jwcxz/bcard/boards/bcard/bcard-brd.png

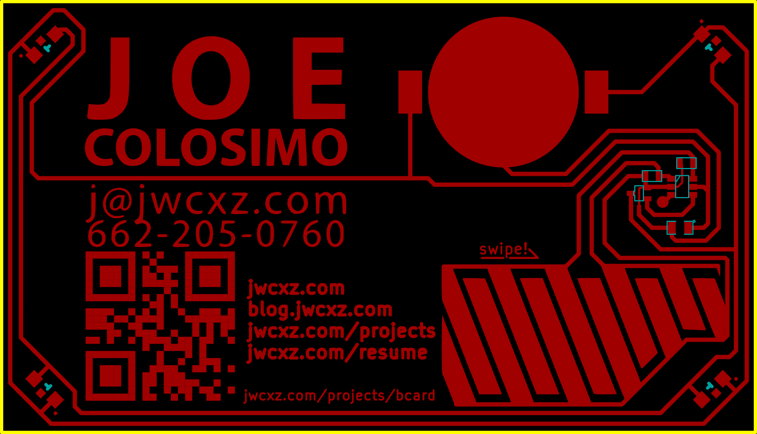
boards/bcard/bcard-brd.png
