jwcxz/bcard/imprint/name-mask.png

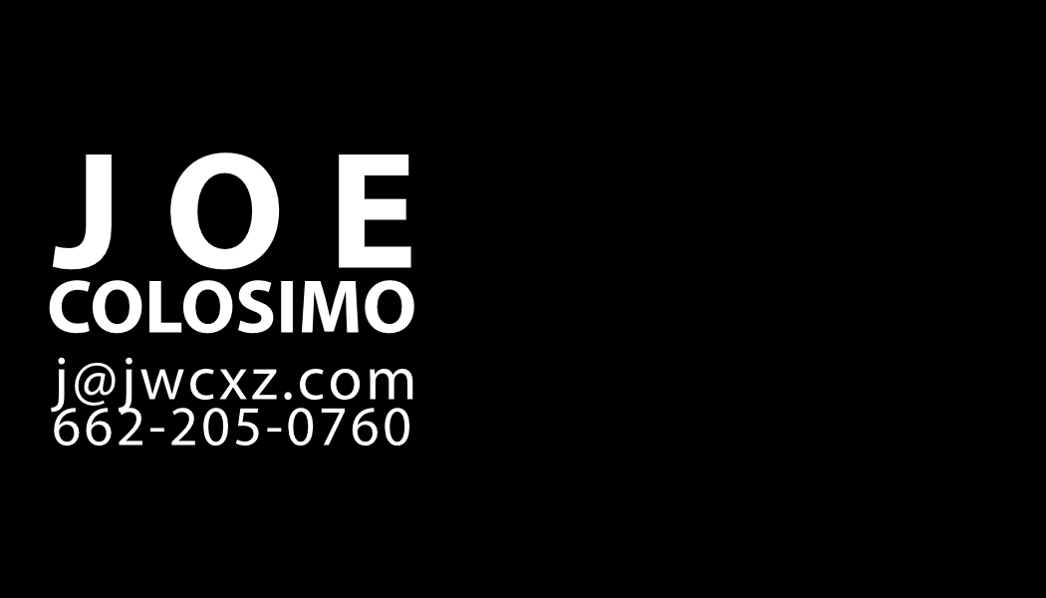
imprint/name-mask.png
