jwcxz/bcard/boards/bcard/bcard-print.png

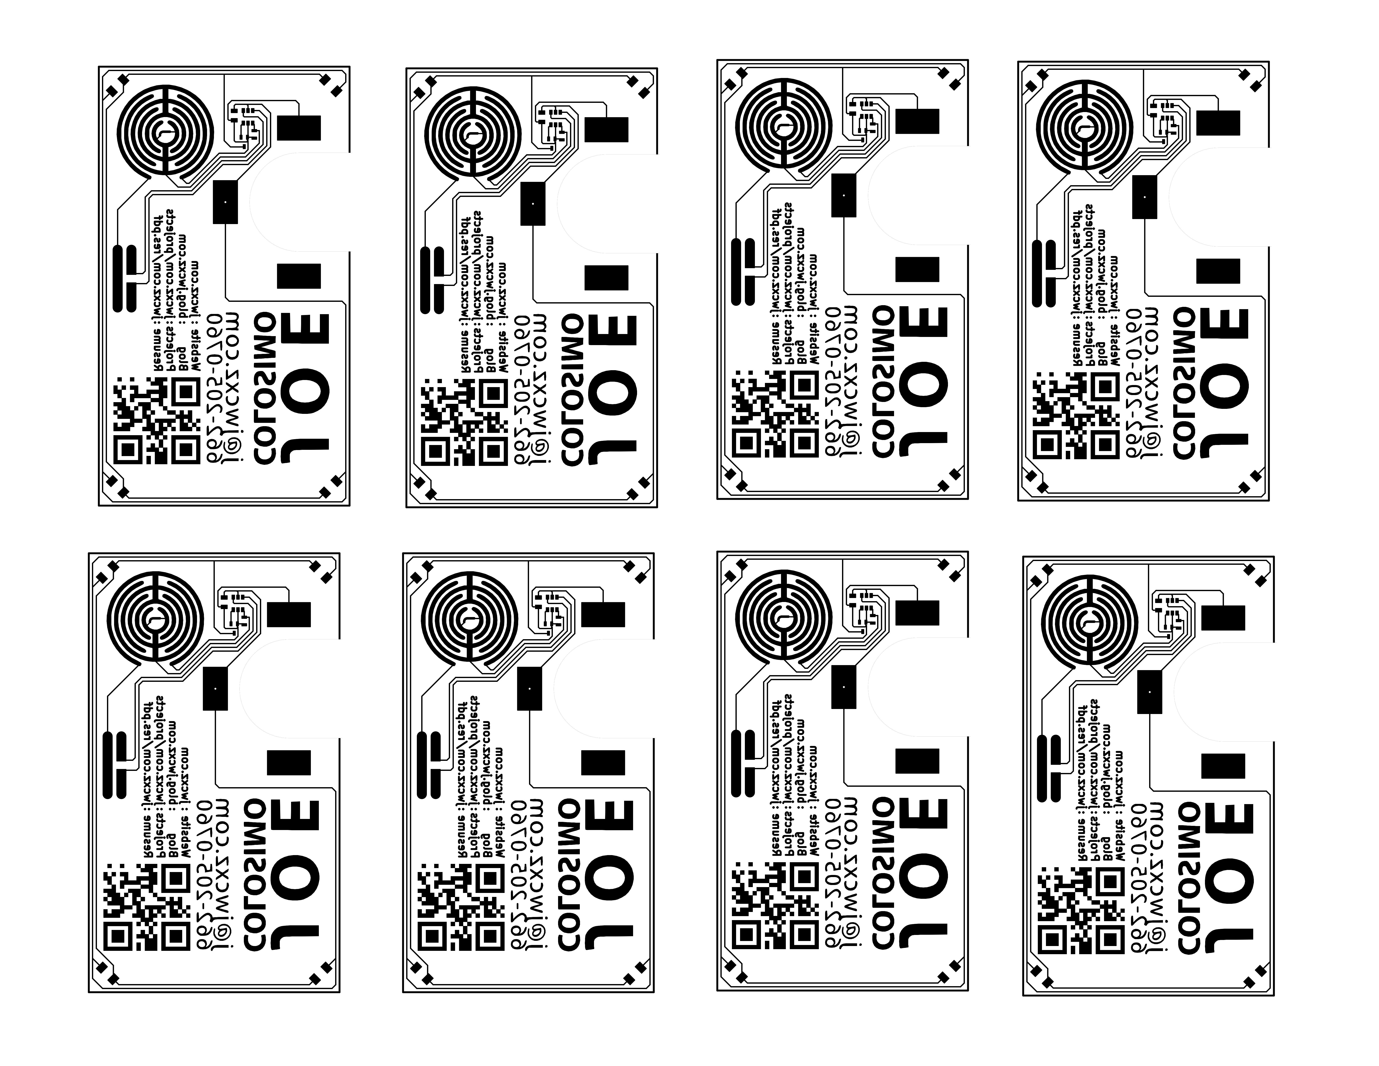
boards/bcard/bcard-print.png
