jwcxz/bcard/boards/bcard/bcard.sch

## KiCad design boards/bcard/bcard.sch (2012-07-29)

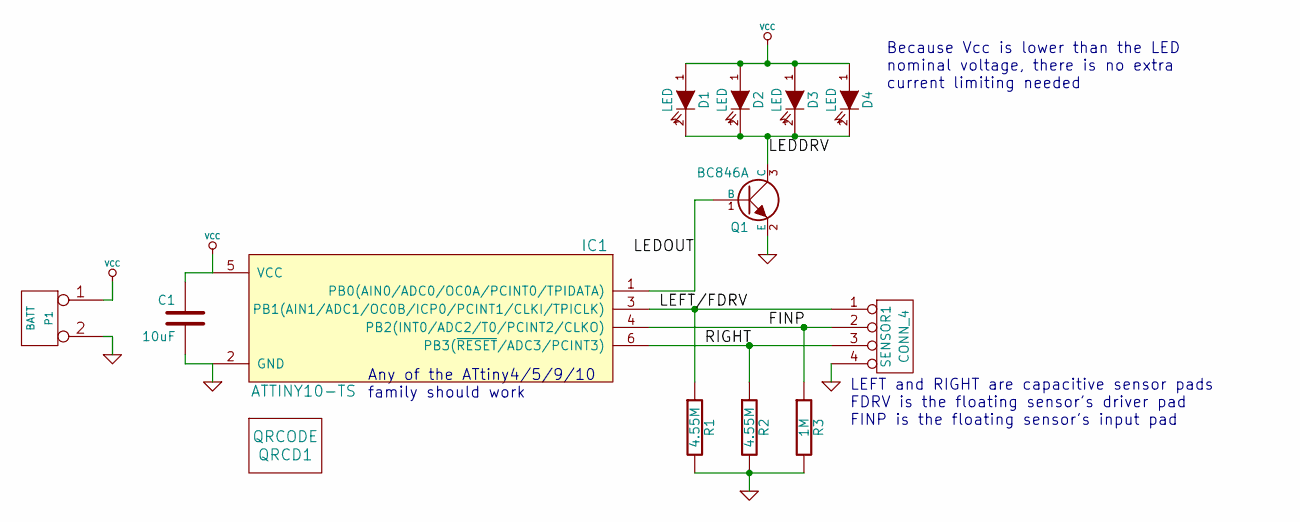
[picture p15: schematic bcard.sch]

Parts:
C1: 10uF; SM0805; Part GRM21BR60J106KE19L
D1, D2, D3, D4: LED; 1208vert; Part APT3216QBC/D
IC1: ATTINY10-TS; SOT23_6; Part ATTINY10-TSHR
P1: BATT; 2032BATTHOLDER; Part BK-912
Q1: BC846A; SOT23; Part BC846A
QRCD1: QRCODE; JWCXZ
R1, R2: 4.55M; SM0603; Part RC0603JR-071ML
R3: 1M; SM0603; Part RC0603JR-071ML
SENSOR1: CONN_4; SENSOR2

Connections:
FINP: IC1.4 (PB2(INT0/ADC2/T0/PCINT2/CLKO)), R3.1, SENSOR1.2
GND: C1.2, IC1.2 (GND), P1.2 (PM), Q1.2 (E), R1.2, R2.2, R3.2, SENSOR1.4
LEDDRV: D1.2 (K), D2.2 (K), D3.2 (K), D4.2 (K), Q1.3 (C)
LEDOUT: IC1.1 (PB0(AIN0/ADC0/OC0A/PCINT0/TPIDATA)), Q1.1 (B)
LEFT/FDRV: IC1.3 (PB1(AIN1/ADC1/OC0B/ICP0/PCINT1/CLKI/TPI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), R1.1, SENSOR1.1
RIGHT: IC1.6 (PB3(~RESET~/ADC3/PCINT3)), R2.1, SENSOR1.3
VCC: C1.1, D1.1 (A), D2.1 (A), D3.1 (A), D4.1 (A), IC1.5 (VCC), P1.1

Notes on the sheet:
LEFT and RIGHT are capacitive sensor pads FDRV is the floating sensor's driver pad FINP is the floating sensor's input pad
Any of the ATtiny4/5/9/10 family should work
Because Vcc is lower than the LED nominal voltage, there is no extra current limiting needed
