jwcxz/bcard/boards/cftest/cftest.sch

## KiCad design boards/cftest/cftest.sch (2012-08-14)

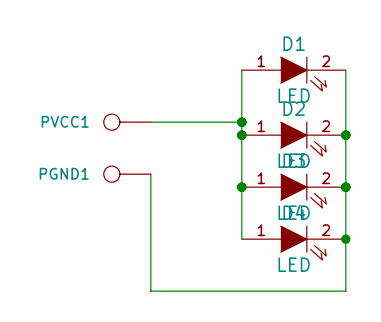
[picture p16: schematic cftest.sch]

Parts:
D1, D2, D3, D4: LED
PGND1: CONN_1
PVCC1: CONN_1

Connections:
unnamed: D1.1 (A), D2.1 (A), D3.1 (A), D4.1 (A), PVCC1.1
unnamed: D1.2 (K), D2.2 (K), D3.2 (K), D4.2 (K), PGND1.1
