jwcxz/bcard/boards/csensebreakout/csensebreakout.sch

## KiCad design boards/csensebreakout/csensebreakout.sch (2012-07-11)

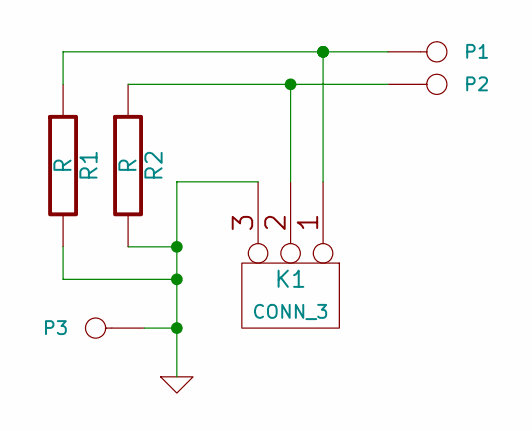
[picture p17: schematic csensebreakout.sch]

Parts:
K1: CONN_3; SENSOR2
P1, P2, P3: CONN_1; PIN
R1, R2: R; SM0603

Connections:
GND: K1.3, P3.1, R1.2, R2.2
unnamed: K1.1, P1.1, R1.1
unnamed: K1.2 (PM), P2.1, R2.1
