jwcxz/bcard/boards/tinybreakout/tinybreakout.sch

## KiCad design boards/tinybreakout/tinybreakout.sch (2012-06-19)

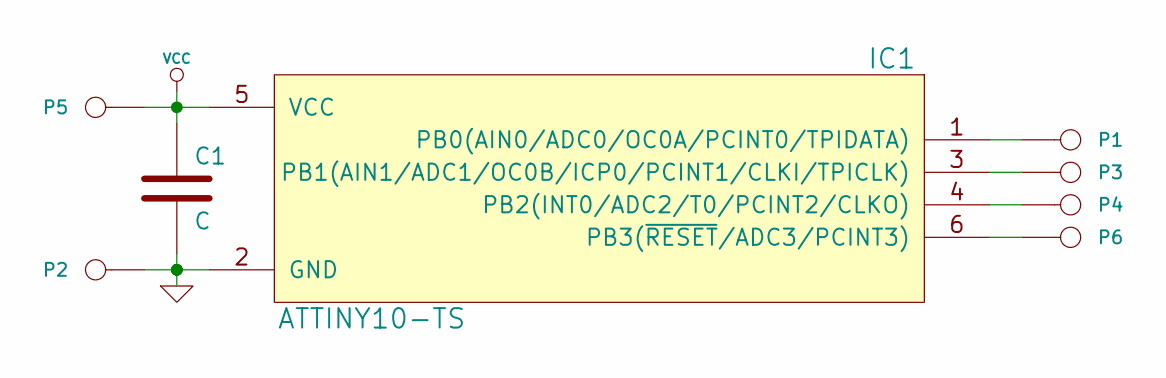
[picture p18: schematic tinybreakout.sch]

Parts:
C1: C
IC1: ATTINY10-TS; SOT23-6
P1, P2, P3, P4, P5, P6: CONN_1

Connections:
GND: C1.2, IC1.2 (GND), P2.1
unnamed: IC1.1 (PB0(AIN0/ADC0/OC0A/PCINT0/TPIDATA)), P1.1
unnamed: IC1.3 (PB1(AIN1/ADC1/OC0B/ICP0/PCINT1/CLKI/TPI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), P3.1
unnamed: IC1.4 (PB2(INT0/ADC2/T0/PCINT2/CLKO)), P4.1
unnamed: IC1.6 (PB3(~RESET~/ADC3/PCINT3)), P6.1
VCC: C1.1, IC1.5 (VCC), P5.1
